minbiocabanon/shieldfoxuino/Olimex/olimex328.jpg

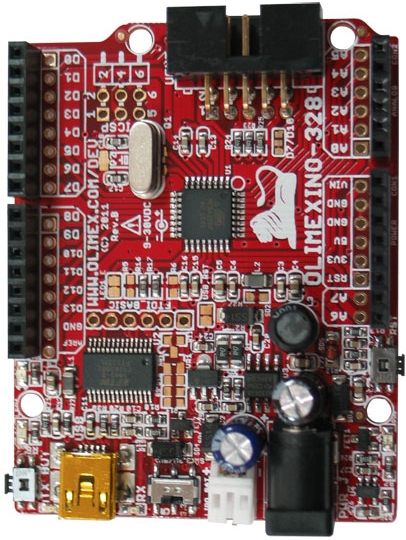
Olimex/olimex328.jpg
