minbiocabanon/shieldfoxuino/utils/Microstrip_50R_869MHz.jpg

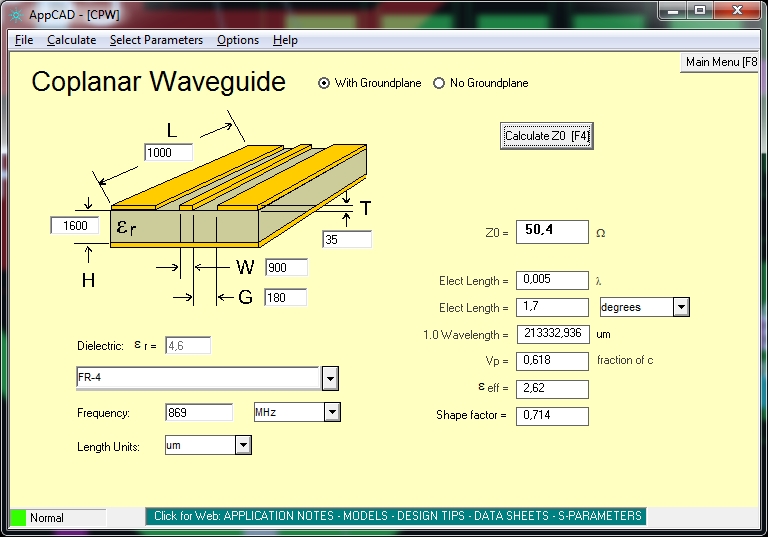
utils/Microstrip_50R_869MHz.jpg
