minbiocabanon/shieldfoxuino/utils/Microstrip_50R_1575MHz.jpg

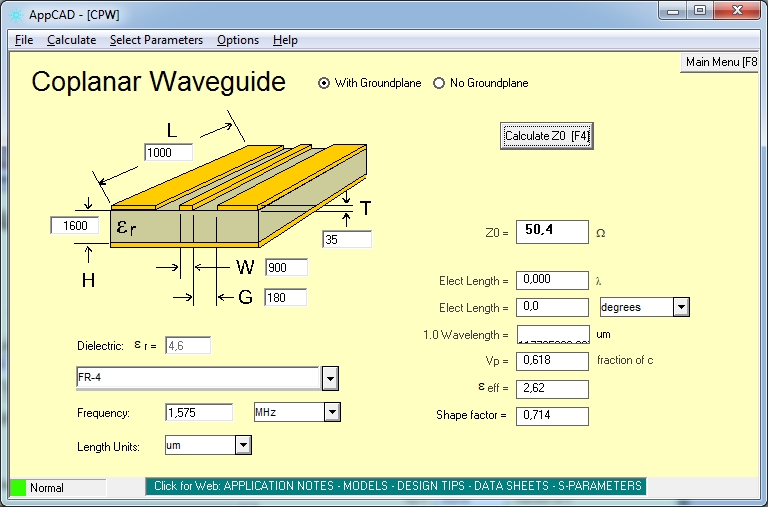
utils/Microstrip_50R_1575MHz.jpg
