minbiocabanon/shieldfoxuino/img/Bureau_test_sigfox_ok.png

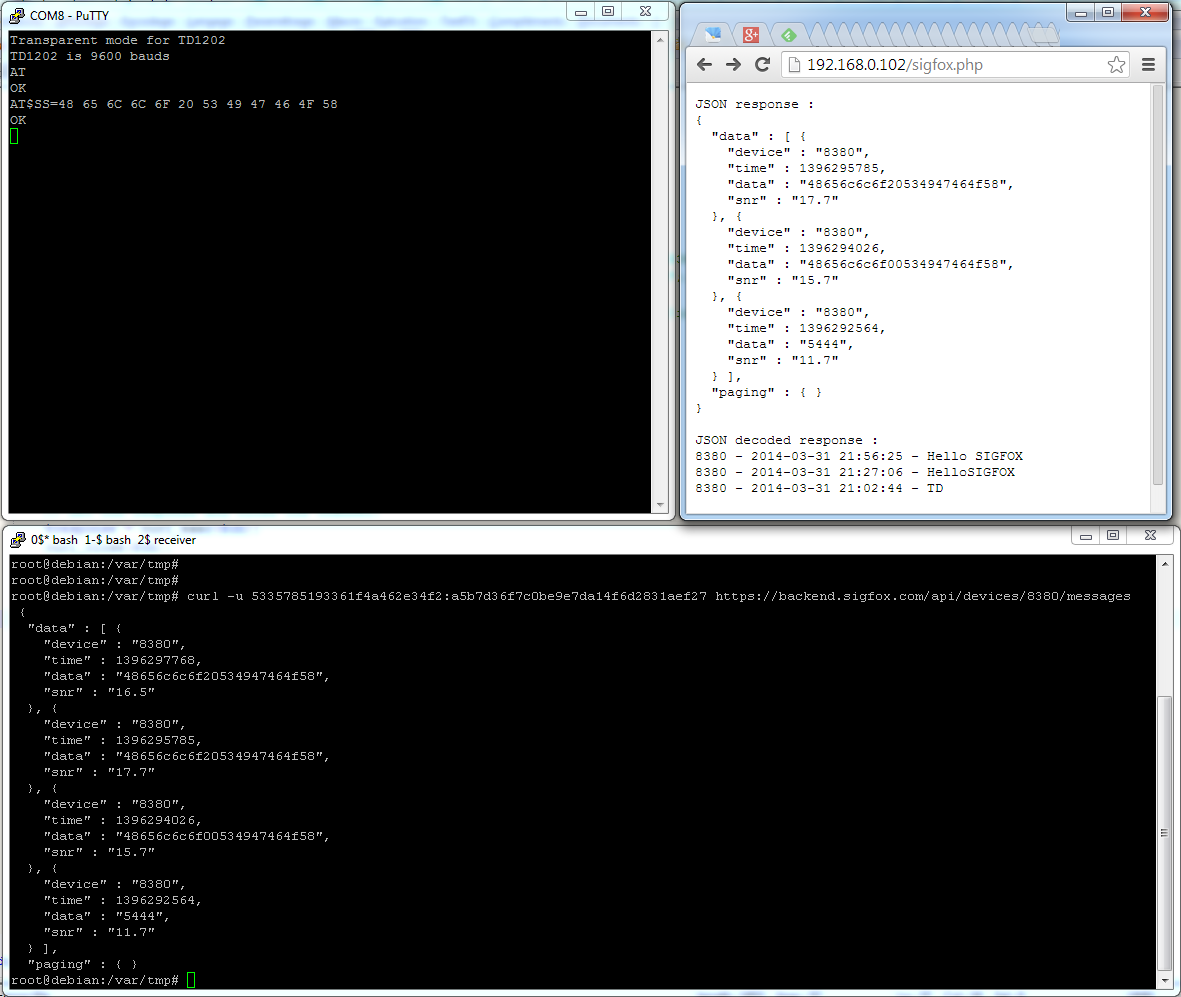
img/Bureau_test_sigfox_ok.png
